Lee-F-Evans/Flex-E-Rex-Soldering-Kit/Images/original_instructions/1.png

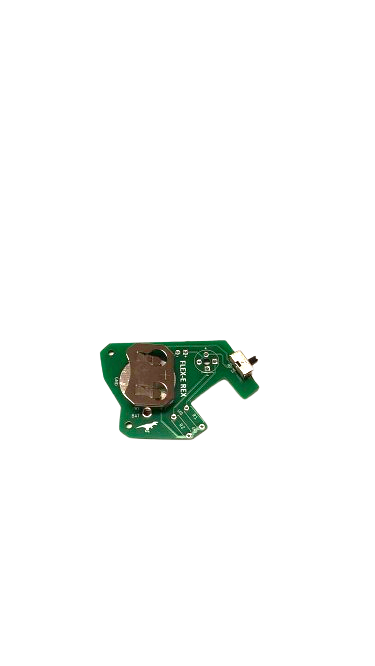
Images/original_instructions/1.png
