Lee-F-Evans/Flex-E-Rex-Soldering-Kit/Images/original_instructions/2.png

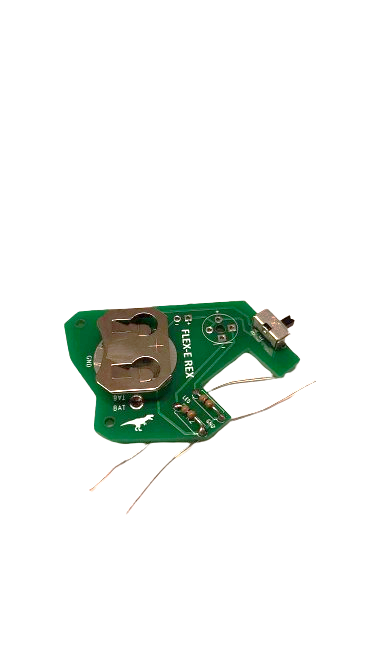
Images/original_instructions/2.png
