Lee-F-Evans/Flex-E-Rex-Soldering-Kit/Images/original_instructions/3a.png

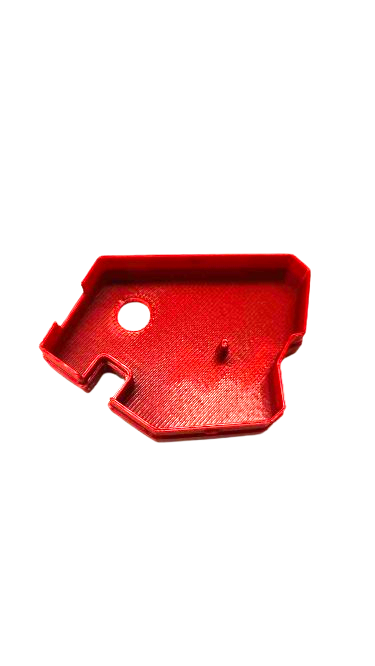
Images/original_instructions/3a.png
