Lee-F-Evans/Flex-E-Rex-Soldering-Kit/Images/original_instructions/3b.png

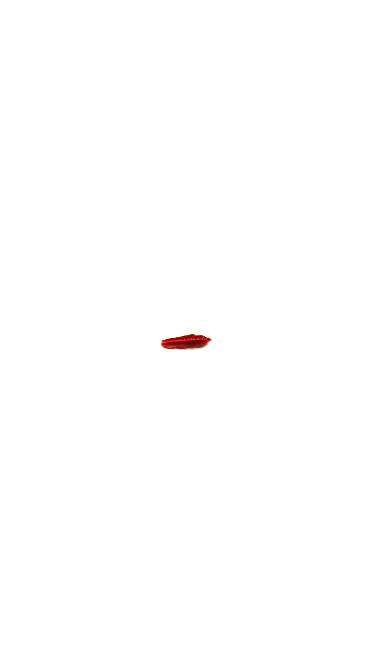
Images/original_instructions/3b.png
