Lee-F-Evans/Flex-E-Rex-Soldering-Kit/Images/original_instructions/7a.png

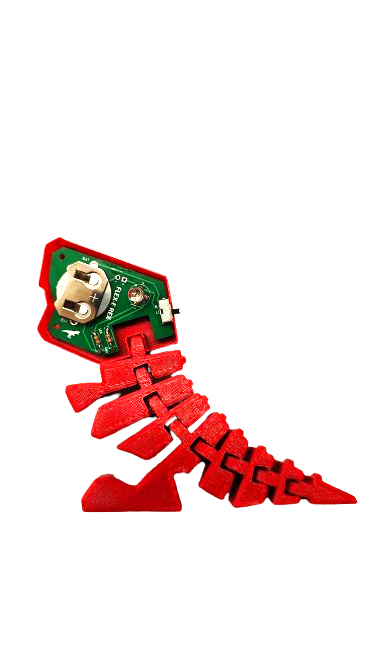
Images/original_instructions/7a.png
