Lee-F-Evans/Flex-E-Rex-Soldering-Kit/Images/original_instructions/7b.png

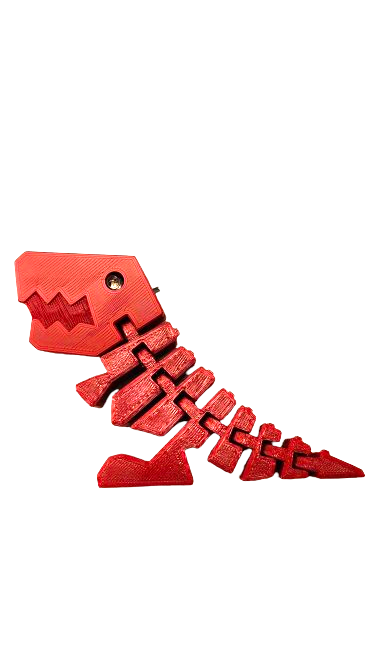
Images/original_instructions/7b.png
