Lee-F-Evans/Flex-E-Rex-Soldering-Kit/Images/original_instructions/+-_of_Led.png

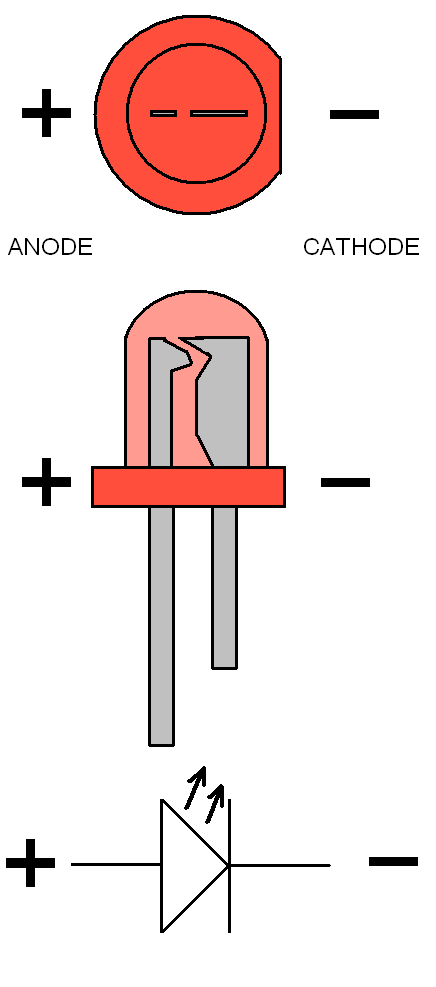
Images/original_instructions/+-_of_Led.png
