Lee-F-Evans/Flex-E-Rex-Soldering-Kit/Images/upscaled_instructions/good solder joints.jpeg

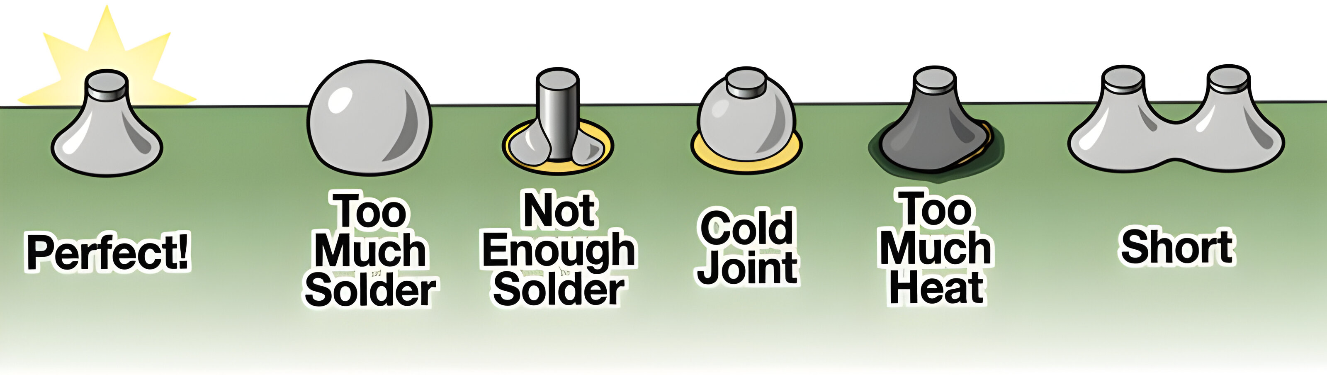
Images/upscaled_instructions/good solder joints.jpeg
